DIYSynthMNL/Eurorack-2164-Quad-Exponential-VCA/kicad/AS2164-Quad-Exponential-VCA.kicad_sch

## KiCad design kicad/AS2164-Quad-Exponential-VCA.kicad_sch (2025-03-11, an earlier design)

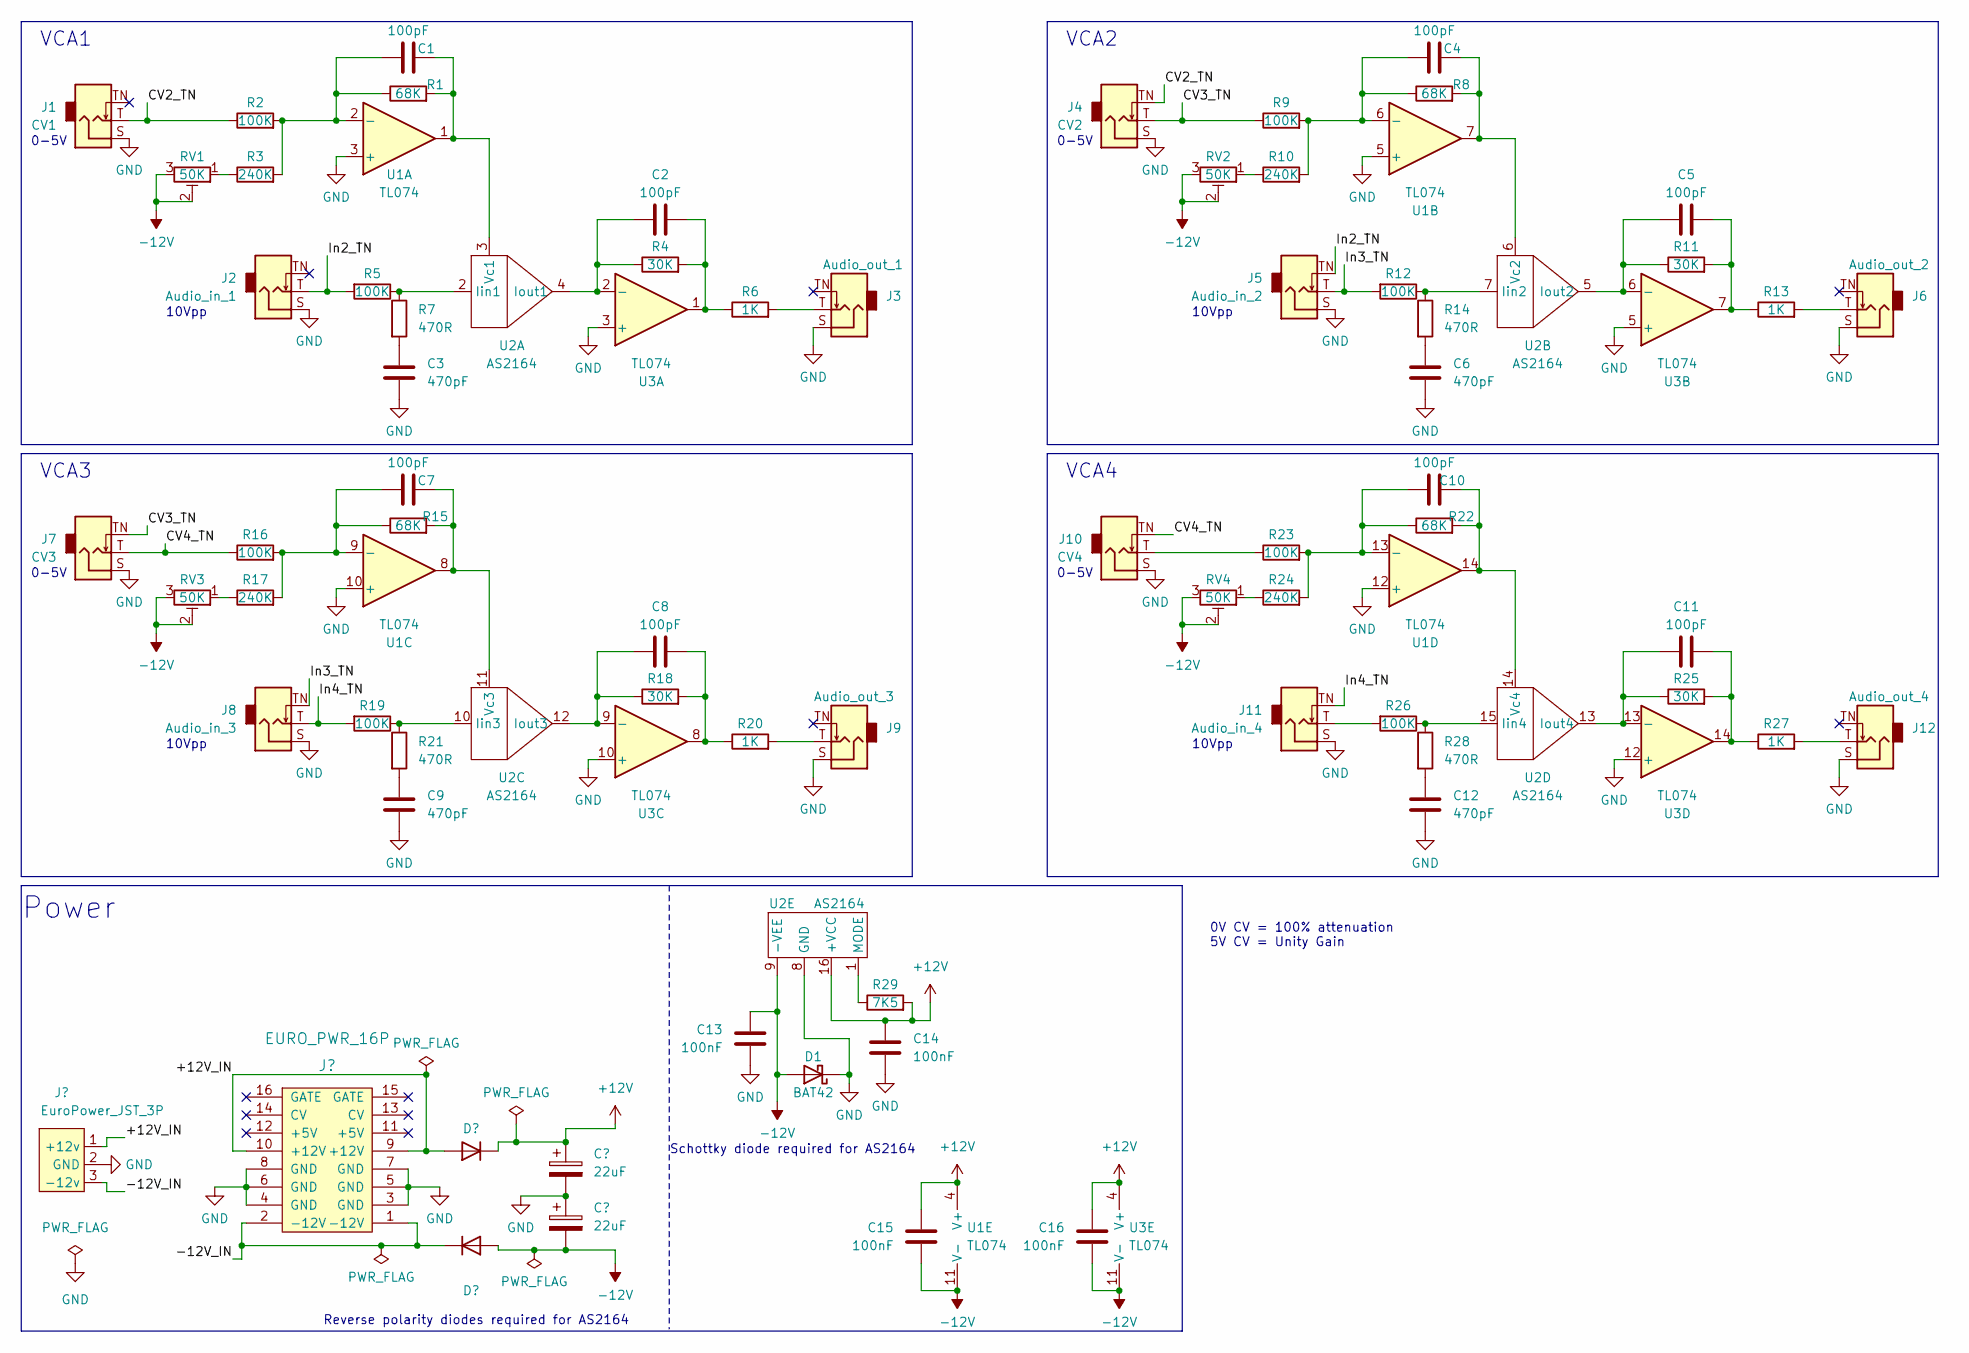
[picture p12: schematic AS2164-Quad-Exponential-VCA.kicad_sch]

Parts:
C1, C2, C4, C5, C7, C8, C10, C11: 100pF
C3, C6, C9, C12: 470pF
C13, C14, C15, C16: 100nF
C17, C18: 22uF; CP_Radial_D4.0mm_P1.50mm
D1: BAT42
D2, D3: D_DO-41_SOD81_P7.62mm_Horizontal_BigPads
J1: CV1; AudioJack_3.5mm_long_pads
J2: Audio_in_1; AudioJack_3.5mm_long_pads
J3: Audio_out_1; AudioJack_3.5mm_long_pads
J4: CV2; AudioJack_3.5mm_long_pads
J5: Audio_in_2; AudioJack_3.5mm_long_pads
J6: Audio_out_2; AudioJack_3.5mm_long_pads
J7: CV3; AudioJack_3.5mm_long_pads
J8: Audio_in_3; AudioJack_3.5mm_long_pads
J9: Audio_out_3; AudioJack_3.5mm_long_pads
J10: CV4; AudioJack_3.5mm_long_pads
J11: Audio_in_4; AudioJack_3.5mm_long_pads
J12: Audio_out_4; AudioJack_3.5mm_long_pads
J13: EuroPower_JST_3P; Eurorack_power_jst_3P
J14: EURO_PWR_16P; IDC-Header_2x08_P2.54mm_Vertical
R1, R8, R15, R22: 68K
R2, R5, R9, R12, R16, R19, R23, R26: 100K
R3, R10, R17, R24: 240K
R4, R11, R18, R25: 30K
R6, R13, R20, R27: 1K
R7, R14, R21, R28: 470R
R29: 7K5
RV1, RV2, RV3, RV4: 50K
U1, U3: TL074
U2: AS2164

Connections:
+12V: C14.1, C15.1, C16.1, C17.1, D2.1 (K), R29.2, U1.4 (V+), U2.16 (+VCC), U3.4 (V+)
+12V_IN: D2.2 (A), J13.1 (+12v), J14.9 (+12V), J14.10 (+12V)
-12V: C13.1, C15.2, C16.2, C18.2, D1.2 (A), D3.2 (A), RV1.2, RV1.3, RV2.2, RV2.3, RV3.2, RV3.3, RV4.2, RV4.3, U1.11 (V-), U2.9 (-VEE), U3.11 (V-)
-12V_IN: D3.1 (K), J13.3 (-12v), J14.1 (-12V), J14.2 (-12V)
CV2_TN: J1.T, J4.TN, R2.1
CV3_TN: J4.T, J7.TN, R9.1
CV4_TN: J7.T, J10.TN, R16.1
GND: C3.2, C6.2, C9.2, C12.2, C13.2, C14.2, C17.2, C18.1, D1.1 (K), J1.S, J2.S, J3.S, J4.S, J5.S, J6.S, J7.S, J8.S, J9.S, J10.S, J11.S, J12.S, J13.2 (GND), J14.3 (GND), J14.4 (GND), J14.5 (GND), J14.6 (GND), J14.7 (GND), J14.8 (GND), U1.3 (+), U1.5 (+), U1.10 (+), U1.12 (+), U2.8 (GND), U3.3 (+), U3.5 (+), U3.10 (+), U3.12 (+)
In2_TN: J2.T, J5.TN, R5.2
In3_TN: J5.T, J8.TN, R12.2
In4_TN: J8.T, J11.TN, R19.2
unnamed: C1.1, R1.1, R2.2, R3.2, U1.2 (-)
unnamed: C1.2, R1.2, U1.1, U2.3 (Vc1)
unnamed: C2.1, R4.1, U2.4 (Iout1), U3.2 (-)
unnamed: C2.2, R4.2, R6.1, U3.1
unnamed: C3.1, R7.2
unnamed: C4.1, R8.1, R9.2, R10.2, U1.6 (-)
unnamed: C4.2, R8.2, U1.7, U2.6 (Vc2)
unnamed: C5.1, R11.1, U2.5 (Iout2), U3.6 (-)
unnamed: C5.2, R11.2, R13.1, U3.7
unnamed: C6.1, R14.2
unnamed: C7.1, R15.1, R16.2, R17.2, U1.9 (-)
unnamed: C7.2, R15.2, U1.8, U2.11 (Vc3)
unnamed: C8.1, R18.1, U2.12 (Iout3), U3.9 (-)
unnamed: C8.2, R18.2, R20.1, U3.8
unnamed: C9.1, R21.2
unnamed: C10.1, R22.1, R23.2, R24.2, U1.13 (-)
unnamed: C10.2, R22.2, U1.14, U2.14 (Vc4)
unnamed: C11.1, R25.1, U2.13 (Iout4), U3.13 (-)
unnamed: C11.2, R25.2, R27.1, U3.14
unnamed: C12.1, R28.2
unnamed: J3.T, R6.2
unnamed: J6.T, R13.2
unnamed: J9.T, R20.2
unnamed: J10.T, R23.1
unnamed: J11.T, R26.2
unnamed: J12.T, R27.2
unnamed: R3.1, RV1.1
unnamed: R5.1, R7.1, U2.2 (Iin1)
unnamed: R10.1, RV2.1
unnamed: R12.1, R14.1, U2.7 (Iin2)
unnamed: R17.1, RV3.1
unnamed: R19.1, R21.1, U2.10 (Iin3)
unnamed: R24.1, RV4.1
unnamed: R26.1, R28.1, U2.15 (Iin4)
unnamed: R29.1, U2.1 (MODE)

Notes on the sheet:
0-5V
0V CV = 100% attenuation 5V CV = Unity Gain
10Vpp
Power
VCA3
VCA2
VCA1
VCA4
Schottky diode required for AS2164
Reverse polarity diodes required for AS2164
